shaoxiongduan/sci-calc/games/CatacombsOfTheDamned/Images.inc.h

/*unsigned char const background[] PROGMEM =
{
	32, 24,

	0x3e, 0x00, 0x3e, 0x7f, 0x7f, 0x7f, 0x7f, 0x7f,
	0x3e, 0x00, 0x3e, 0x7f, 0xff, 0xff, 0x7f, 0x7f,
	0x3e, 0x00, 0x2a, 0x55, 0x2a, 0x55, 0x2a, 0x55,
	0x2a, 0x00, 0x3e, 0x7f, 0x7f, 0x7f, 0x7f, 0x7f,
	0x7f, 0x7f, 0x7f, 0x7f, 0x3e, 0x00, 0x2a, 0x55,
	0x2a, 0x55, 0x2a, 0x54, 0x00, 0x3e, 0x7f, 0x7f,
	0x7f, 0x7f, 0xbe, 0x80, 0xbe, 0xbf, 0x3f, 0x7f,
	0x7f, 0x7f, 0x7f, 0x7f, 0x3e, 0x00, 0x3e, 0x7f,
	0x00, 0x3e, 0x7f, 0x7f, 0x7f, 0x7f, 0x7f, 0x3e,
	0x00, 0x3e, 0x7f, 0x7f, 0x7f, 0x7f, 0x3e, 0x00,
	0x3e, 0x7f, 0x7f, 0x7f, 0x7f, 0x7f, 0x7f, 0x3e,
	0x00, 0x2a, 0x55, 0x2a, 0x55, 0x2a, 0x55, 0x2a,
};*/

unsigned char const background[] PROGMEM =
{
	64, 24,
	0x7f, 0xff, 0x7f, 0xff, 0x7f, 0xff, 0x3f, 0xdf,
	0xef, 0xda, 0x3f, 0xff, 0x7f, 0xff, 0x7f, 0xff,
	0x7f, 0xff, 0x7f, 0xff, 0x7f, 0xff, 0x7f, 0xff,
	0x7f, 0xaa, 0x7f, 0xff, 0x7f, 0xff, 0x7f, 0xff,
	0x7f, 0xff, 0x7f, 0xfe, 0x7d, 0xfb, 0x57, 0xff,
	0xff, 0xff, 0xff, 0xff, 0xff, 0xff, 0x57, 0xfb,
	0x7d, 0xfe, 0x7f, 0xff, 0x7f, 0xff, 0x7f, 0xff,
	0x7f, 0xaa, 0x7f, 0xff, 0x7f, 0xff, 0x7f, 0xff,
	0x55, 0xff, 0x7f, 0xff, 0x7f, 0xff, 0x7e, 0xf9,
	0x40, 0xf9, 0x7e, 0xff, 0x7f, 0xff, 0x7f, 0xff,
	0x55, 0xff, 0x7f, 0xff, 0x7f, 0xff, 0x7f, 0xff,
	0x7f, 0xff, 0x7f, 0xff, 0x7f, 0xff, 0x7f, 0xff,
	0x55, 0xff, 0x7f, 0xff, 0x7f, 0xff, 0x55, 0xff,
	0xff, 0xff, 0xff, 0xff, 0xff, 0xff, 0x55, 0xff,
	0x55, 0xff, 0x7f, 0xff, 0x7f, 0xff, 0x7f, 0xff,
	0x7f, 0xff, 0x7f, 0xff, 0x7f, 0xff, 0x7f, 0xff,
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
	0x25, 0x25, 0xc5, 0x11, 0xff, 0xff, 0xff, 0xff,
	0xfc, 0xfd, 0xfd, 0xfd, 0xfc, 0xfc, 0xfd, 0xfc,
	0xfc, 0xfd, 0xfc, 0xfd, 0xfc, 0xfc, 0xfd, 0xfc,
	0xfd, 0xfc, 0xfc, 0xfd, 0xfc, 0xfd, 0xfd, 0xfd,
	0xfd, 0xfc, 0xfd, 0xfc, 0xfc, 0xfd, 0xfc, 0xfd,
	0xfd, 0xfd, 0xfc, 0xfe, 0xff, 0xff, 0xff, 0xff,
};
