shaoxiongduan/sci-calc/games/CatacombsOfTheDamned/Sounds.cpp

#include "Sounds.h"

#define TONES_END 0x8000

const uint16_t Sounds::Attack[] PROGMEM = {
	0x0131,0x0007,0x0000,0x0015,0x018d,0x0007,0x0000,0x0007,0x033c,0x0007,0x0219,0x0007,0x0238,0x0007,0x025a,0x0007,0x0080,0x0007,0x025a,0x001d,0x007e,
	0x0007,0x025a,0x0007,0x0238,0x0007,0x0228,0x0007,0x0219,0x0007,0x007d,0x000e,0x018d,0x0007,0x0128,0x0007,0x0120,0x0007,0x00f8,0x0007,0x00ef, 
	0x0007,0x007d,0x0007,0x00ac,0x0007,0x009b,0x0007,0x0093,0x0007,0x008e,0x0007,0x008b,0x0007,0x0087,0x0007,0x0084,0x0007,0x007d,0x0007,0x0081,
	0x0007,//0x0080,0x0007,0x007e,0x0007,0x007d,0x0007,0x007c,0x000e,0x0000,0x000e,0x008d,0x0007,0x0000,0x0015,0x0087,0x0007,0x0000,0x000e,0x0085,
	//0x0007,0x0083,0x0007,0x0000,0x0024,0x008c,0x0007,0x0081,0x000e,0x0000,0x0007,0x008d,0x0007,0x0000,0x002b,0x0083,0x000e, 
	TONES_END
};

const uint16_t Sounds::Kill[] PROGMEM = {
	0x0151,0x0007,0x0000,0x0015,0x018d,0x0007,0x0000,0x0007,0x014b,0x0007,0x0136,0x0007,0x0146,0x0007,0x0169,0x0007,0x019e,0x0007,0x007f,0x0007,0x0185,
	0x0007,0x0228,0x0007,0x026d,0x0007,0x02fc,0x0007,0x02e0,0x0007,0x01fd,0x0007,0x0219,0x0007,0x033c,0x0007,0x00e7,0x0007,0x0281,0x0007,0x026d,
	0x000e,0x052d,0x000e,0x04da,0x000e,0x011c,0x0007,0x0387,0x0007,0x0360,0x0007,0x033c,0x0007,0x0387,0x0007,0x02ad,0x000e,0x02c6,0x0007,0x010c,
	0x000e,0x02e0,0x0007,0x02c6,0x0007,0x0296,0x000e,0x0281,0x0007,0x02ad,0x0007,0x02c6,0x0007,0x02e0,0x0007,0x00e1,0x0007,0x031b,0x0007,0x0248,
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
	0x0007,0x007d,0x0007,0x007e,0x0007,0x0093,0x0007,0x007e,0x0007,0x0000,0x0007,0x0089,0x0007,0x0085,0x0007,0x0082,0x0007,0x0080,0x0007,0x007e,
	0x0007,0x007d,0x0007, TONES_END
};
