shaoxiongduan/sci-calc/games/snake-game/fruit.h

#pragma once

#include "snake.h"
#include "position.h"

class Fruit {
  public:
    Fruit(Snake * snake);
    void randomize(Snake * snake);
    const Position getPosition();
  private:
    Position position { Position(0, 0) };
};
