shaoxiongduan/sci-calc/sci_calc_code/src/UIElements/BinLink.h

#ifndef BIN_LINK_H
#define BIN_LINK_H

#include "../Animation/Animation.h"

class BinLink : public UIElement {
    public: 
        BinLink(std::string path);

        void activate();

        void draw();

        void update();

    private:
        std::string path;
}; 

#endif
